mhorimoto/M302N/3DPRN/PCB-model-Base-BodySketch.dxf

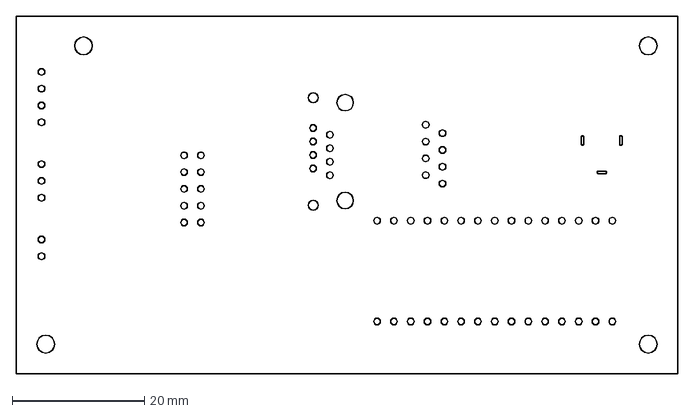
[picture p21: CAD file, 2025-03-06]
3DPRN/PCB-model-Base-BodySketch.dxf
100.0 x 54.0 mm
