mhorimoto/M302N/M302N.kicad_pcb

## KiCad design M302N.kicad_pcb (2025-08-29)

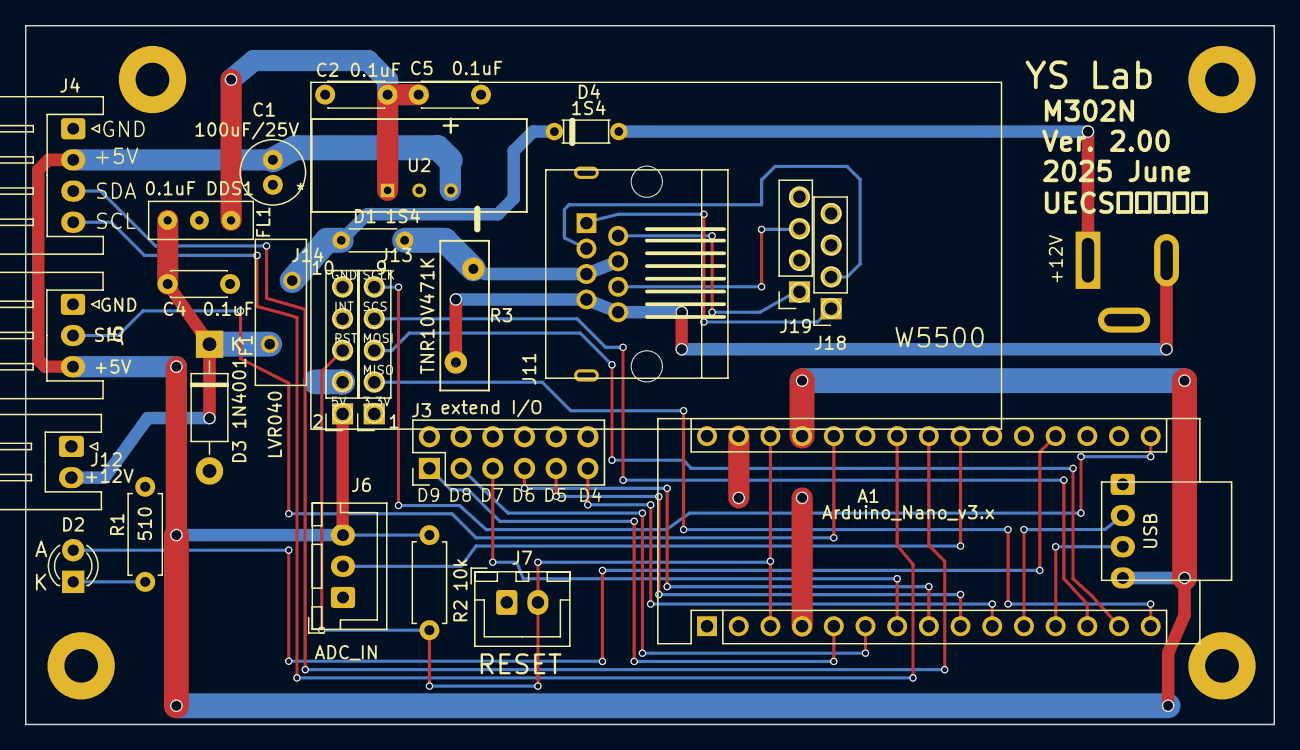
[picture p31: board M302N.kicad_pcb from above]

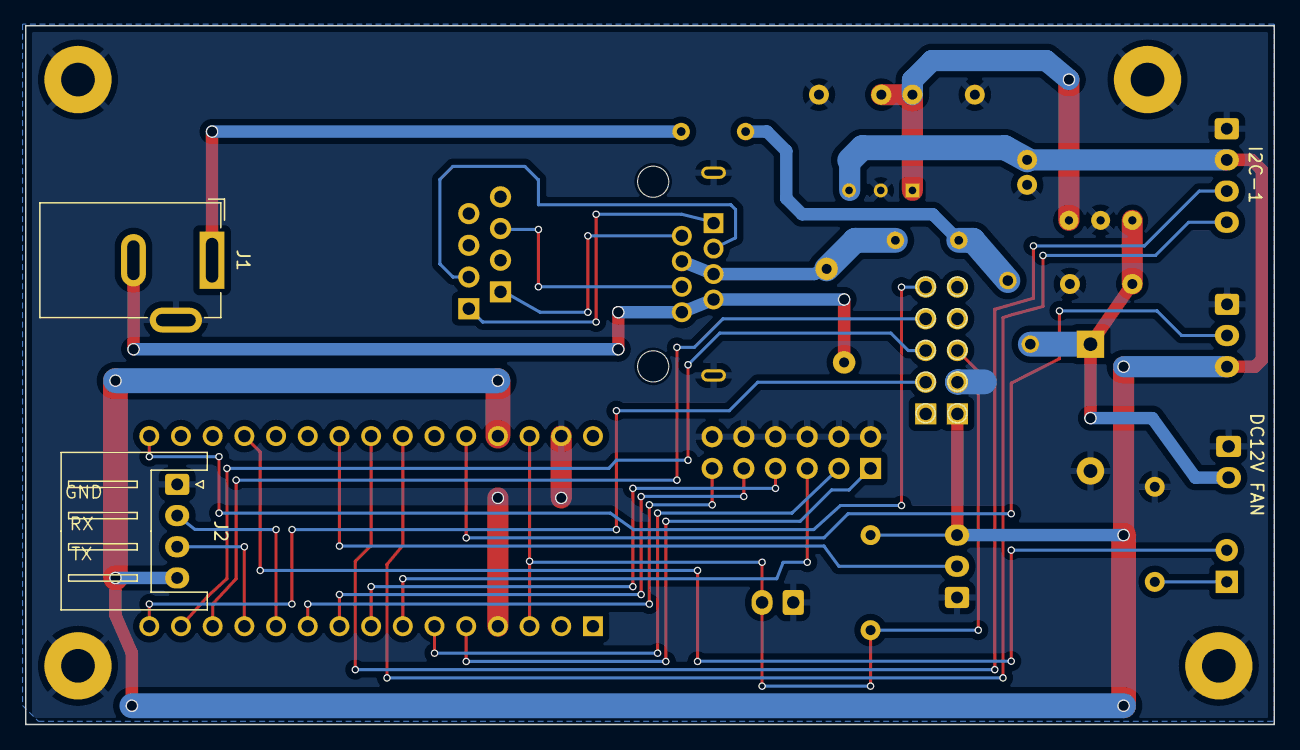
[picture p32: board M302N.kicad_pcb from below]

Board: 2 copper layers, 100.1 x 56.0 mm, 29 parts (2 on the bottom side), 31 nets.

Parts:
A1: Arduino_Nano_v3.x; Arduino_Nano
C1: 100uF/25V; C_Radial_D5.0mm_H11.0mm_P2.00mm
C2, C4, C5: 0.1uF; C_Disc_D4.3mm_W1.9mm_P5.00mm
D1, D4: 1S4; R_Axial_DIN0204_L3.6mm_D1.6mm_P5.08mm_Horizontal
D2: LED; LED_D3.0mm
D3: 1N4001; D_DO-41_SOD81_P10.16mm_Horizontal
F1: LVR040; Fuse_BelFuse_0ZRE0033FF_L11.4mm_W3.8mm
FL1: 0.1uF DDS1; DSS1
J1: DC12V; BarrelJack_GCT_DCJ200-10-A_Horizontal
J2: UART; JST_XH_S4B-XH-A_1x04_P2.50mm_Horizontal
J3: extend I/O; PinHeader_2x06_P2.54mm_Vertical
J4: I2C-1; JST_XH_S4B-XH-A_1x04_P2.50mm_Horizontal
J5: ADC_IN; JST_XH_S3B-XH-A_1x03_P2.50mm_Horizontal
J6: ADC_IN; JST_XH_B3B-XH-A_1x03_P2.50mm_Vertical
J7: RESET; JST_XH_B2B-XH-A_1x02_P2.50mm_Vertical
J11: RJ45; RJ45_Neltron_7810-8P8C
J12: DC12V FAN; JST_XH_S2B-XH-A_1x02_P2.50mm_Horizontal
J13, J14: Conn_01x05_Socket; PinSocket_1x05_P2.54mm_Vertical
J18, J19: Conn_01x04_Socket; PinSocket_1x04_P2.54mm_Vertical
R1: 510; R_Axial_DIN0207_L6.3mm_D2.5mm_P7.62mm_Horizontal
R2: 10k; R_Axial_DIN0207_L6.3mm_D2.5mm_P7.62mm_Horizontal
R3: TNR10V471K; RV_Disc_D12mm_W3.9mm_P7.5mm
U1: W5500; W5500LARGE
U2: BP5293-50; SIP03_BP5293_17X7P2_ROM

Connections:
+5V: A1.27 (+5V), C1.1, J2.4, J4.2, J5.3, J6.3, J14.1, R2.1, U2.3 (VOUT)
/*D10/SS: A1.13 (D10), J13.4
/*D11/MOSI: A1.14 (D11), J13.3
/+12V: D1.1 (K), D4.1 (K), F1.2
/A4/SDA: A1.23 (A4), J4.3
/A5/SCL: A1.24 (A5), J4.4
/D12/MISO: A1.15 (D12), J13.2
/RX: A1.11 (D8), J2.2
/TX: A1.12 (D9), J2.3
/~RESET: A1.3 (~RESET), A1.28 (~RESET), J7.2, J14.3, R2.2
GND: A1.4 (GND), A1.29 (GND), C1.2, C2.2, C4.2, C5.2, D3.2 (A), FL1.2, J1.3, J2.1, J3.2, J3.4, J3.6, J3.8, J3.10, J3.12, J4.1, J5.1, J6.1, J7.1, J12.1, J14.2, R1.2, U2.2 (GND)
unnamed: A1.19 (A0), D2.2 (A)
unnamed: A1.22 (A3), J6.2
unnamed: A1.26 (A7), J5.2
unnamed: A1.5 (D2), J3.1
unnamed: A1.6 (D3), J3.3
unnamed: A1.7 (D4), J3.5
unnamed: A1.8 (D5), J3.7
unnamed: A1.9 (D6), J3.9
unnamed: A1.10 (D7), J3.11
unnamed: A1.16 (D13), J13.5
unnamed: D1.2 (A), J11.4, J11.5, R3.2
unnamed: D2.1 (K), R1.1
unnamed: C4.1, D3.1 (K), F1.1, FL1.3, J12.2
unnamed: D4.2 (A), J1.1
unnamed: J1.2, J11.7, J11.8, R3.1
unnamed: J11.1, J18.1
unnamed: J11.3, J18.2
unnamed: J11.2, J19.1
unnamed: J11.6, J19.3
unnamed: C2.1, C5.1, FL1.1, U2.1 (VIN)
